HeinrichG-V12/Dual_WBO/software/Dual_WBO_C/Dual_WBO/pid/pid.c

/*
 * pid.c
 *
 * Created: 03.05.2022 17:02:57
 *  Author: Heinrich
 */ 

#include "pid.h"

uint16_t pid_control (uint16_t inputValue, uint16_t UR_calibration)
{
	//Calculate error term.
	uint16_t error = UR_calibration - inputValue;
	
	//Set current position.
	uint16_t position = inputValue;
	
	//Calculate proportional term.
	float pTerm = -pGain * error;
	
	//Calculate the integral state with appropriate limiting.
	iState += error;
	
	if (iState > iMax) iState = iMax;
	if (iState < iMin) iState = iMin;
	
	//Calculate the integral term.
	float iTerm = -iGain * iState;
	
	//Calculate the derivative term.
	float dTerm = -dGain * (dState - position);
	dState = position;
	
	//Calculate regulation (PI).
	uint16_t RegulationOutput = pTerm + iTerm + dTerm;
	
	//Set maximum heater output (full power).
	if (RegulationOutput > pwmMax) RegulationOutput = pwmMax;
	
	//Set minimum heater value (cooling).
	if (RegulationOutput < pwmMin) RegulationOutput = pwmMin;

	//Return calculated PWM output.
	return RegulationOutput;
}
