HeinrichG-V12/Dual_WBO/software/DualWBO/DualWBO/spi/spi.cpp

/*
 * spi.cpp
 *
 * Created: 25.01.2023 17:23:31
 *  Author: Heinrich
 */ 

#include "spi.h"

// Define the static Singleton pointer
Spi* Spi::_instance = nullptr;

Spi::Spi()
{
	// enable spi, 2MHz (div 128), master, mode1 (cpol 0, cpha 1)
	SPCR |= (1 << SPE)|(0 << DORD)|(1 << MSTR)|(0 << CPOL)|(1 << CPHA)|(1 << SPR1)|(1 << SPR0);
}


Spi* Spi::getInstance() {
	if (_instance == nullptr) {
		_instance = new Spi();
	}
	return(_instance);
}

uint16_t Spi::spi_readWrite(uint16_t data)
{
	uint8_t byte1, byte2;
	
	SPDR = (data >> 8);
	while(!(SPSR & (1<<SPIF)));
	byte1 = SPDR;
	byte1 &= ~((1 << 7)|(1 << 6));	// clear two most significant bits in control byte because of don't care, cj125 manual, page 16
	SPDR = (data & 0xFF);
	while(!(SPSR & (1<<SPIF)));
	byte2 = SPDR;
	
	return (uint16_t)((byte1<<8)|byte2);
}
