HeinrichG-V12/Dual_WBO/software/DualWBO/DualWBO/helpers.h

/*
 * helpers.h
 *
 * Created: 23.01.2023 17:44:39
 *  Author: Heinrich
 */ 


#ifndef HELPERS_H_
#define HELPERS_H_

#include <stdint.h>
#include <stdbool.h>

static __inline uint16_t __bswap_16(uint16_t __x)
{
	return (__x << 8)|(__x >> 8);
}

static __inline uint16_t __make_u16t(uint8_t __x1, uint8_t __x2)
{
	// return (uint16_t)((__x2 << 8) + (__x1 & 0x00ff));
	return ((uint16_t) __x1 << 8) | __x2;
}

static __inline float __adc2voltage(uint16_t __v)
{
	return ((float) __v * 5UL / 1024UL );
}

static __inline uint16_t __adc2voltage_millis(uint16_t __v)
{
	return ((uint16_t) __v * 5000UL / 1024UL );
}

static __inline uint16_t __voltage2dac_millis (uint16_t millis)
{
	return (uint16_t) (millis * 1024UL / 5000UL);
}

/*
static __inline bool __isSet(uint8_t __x1, uint8_t __x2)
{
	return (__x1 & ( 1 << __x2));
}
*/

static __inline uint8_t __low(uint16_t __x)
{
	return (uint8_t) ((__x) & 0xFF);
}

static __inline uint8_t __high(uint16_t __x)
{
	return (uint8_t) (((__x)>>8) & 0xFF);
}

static __inline uint16_t __voltage2duty_cycle(uint16_t _targetVoltageMillis, uint16_t _supplyVoltageMillis, uint16_t _steps)
{
	return (uint16_t)(((float)_targetVoltageMillis / (float)_supplyVoltageMillis) * _steps - 1);
}

static __inline uint16_t __duty_cycle2voltage(uint16_t _supplyVoltageMillis, uint16_t _dutyCycle, uint16_t _steps)
{
	return ((float) _supplyVoltageMillis / (float) _steps) *_dutyCycle;
}


static __inline uint8_t __is_between(uint16_t x, uint16_t y, uint16_t z)
{
	if ((x > y) && (x < z))
	{
		return 1;
	}
	
	return 0;
}

#define bswap_16(x) __bswap_16(x)
#define make_u16t(x1,x2) __make_u16t(x1,x2)
#define adc2voltage(adc) __adc2voltage(adc)
#define adc2voltage_millis(adc) __adc2voltage_millis(adc)
#define voltage2dac_millis(millis) __voltage2dac_millis(millis)
#define voltage2duty_cycle(targetVoltage,supplyVoltage,steps) __voltage2duty_cycle(targetVoltage,supplyVoltage,steps)
#define duty_cycle2voltage(supplyVoltage,dutyCycle,steps) __duty_cycle2voltage(supplyVoltage,dutyCycle,steps)
#define is_between(x,y,z) __is_between(x,y,z)

// #define isSet(x1, x2) __isSet(x1, x2)
#define low(x)	__low(x)
#define high(x)	__high(x)


#define bit_set(a,b) ((a) |= (1U<<(b)))
#define bit_clear(a,b) ((a) &= ~(1U<<(b)))
#define bit_check(var,pos) !!((var) & (1U<<(pos)))
#define bit_toggle(var,pos) ((var)^= 1UL << (pos))



#endif /* HELPERS_H_ */
